Arjun-Saini/loop-tracks/images and diagrams/90 right.png

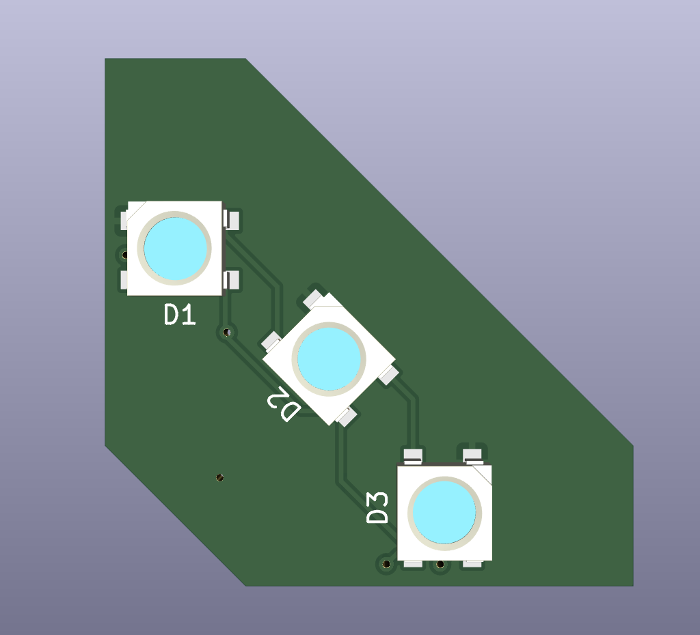
images and diagrams/90 right.png
