Arjun-Saini/loop-tracks/images and diagrams/1.jpeg

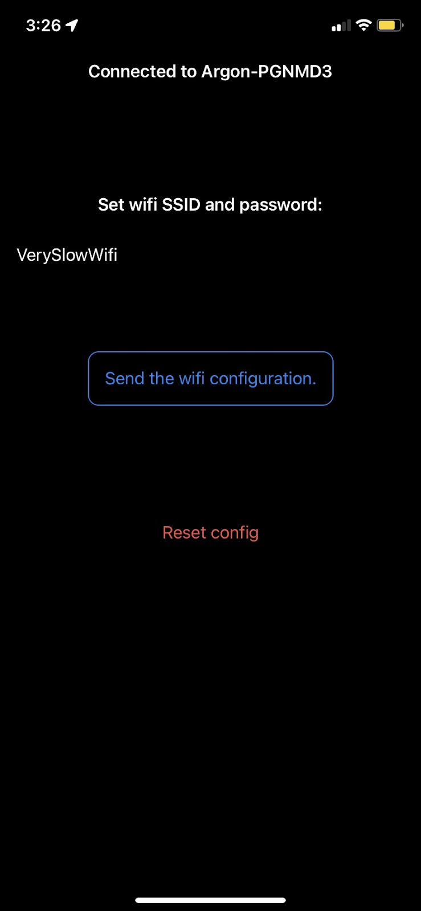
images and diagrams/1.jpeg
