Arjun-Saini/loop-tracks/images and diagrams/2.jpeg

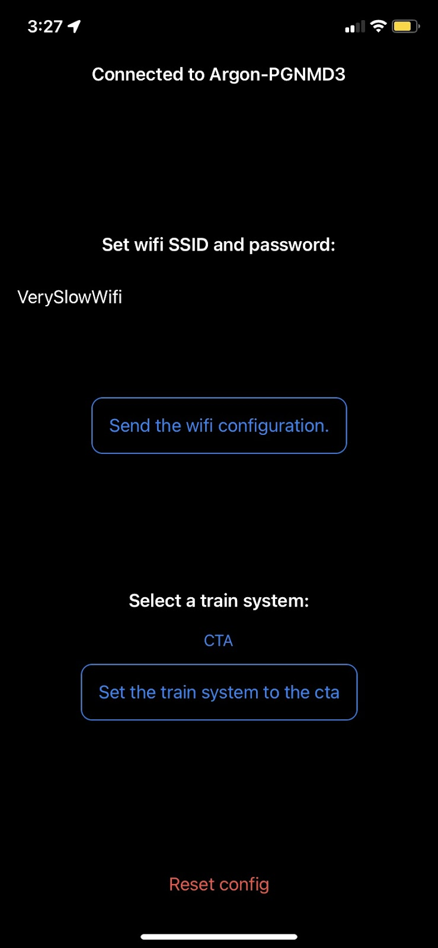
images and diagrams/2.jpeg
