Arjun-Saini/loop-tracks/images and diagrams/3.jpeg

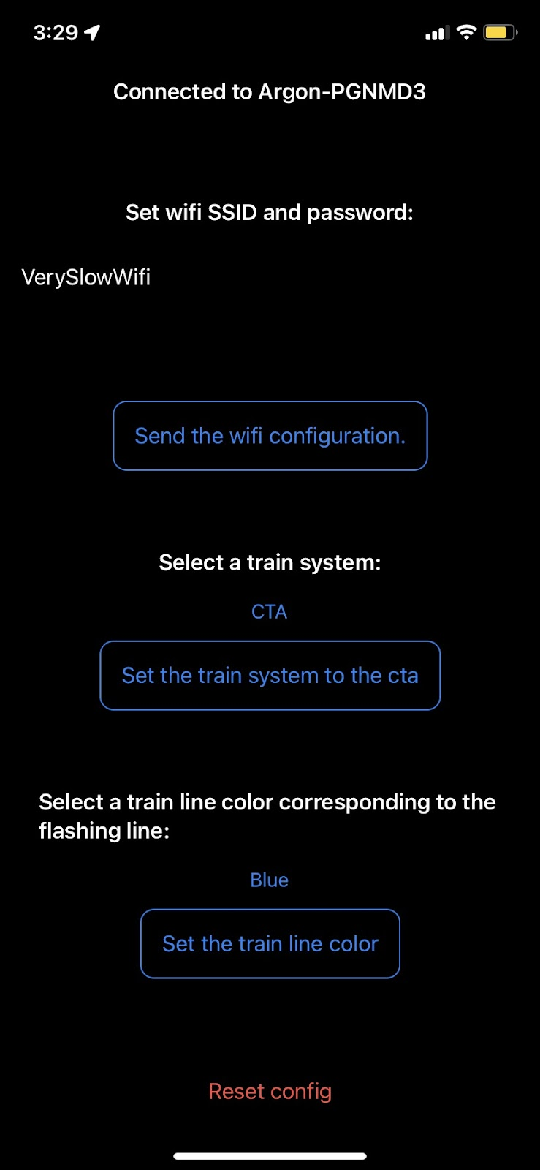
images and diagrams/3.jpeg
