Arjun-Saini/loop-tracks/images and diagrams/90 left.png

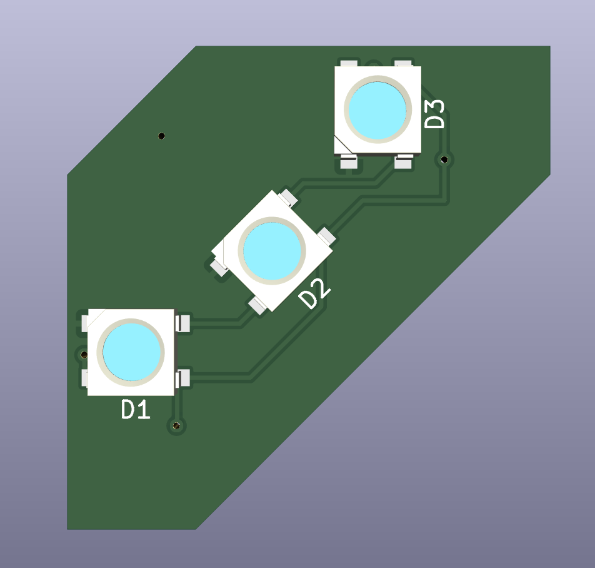
images and diagrams/90 left.png
