Arjun-Saini/loop-tracks/images and diagrams/cta diagram 0.png

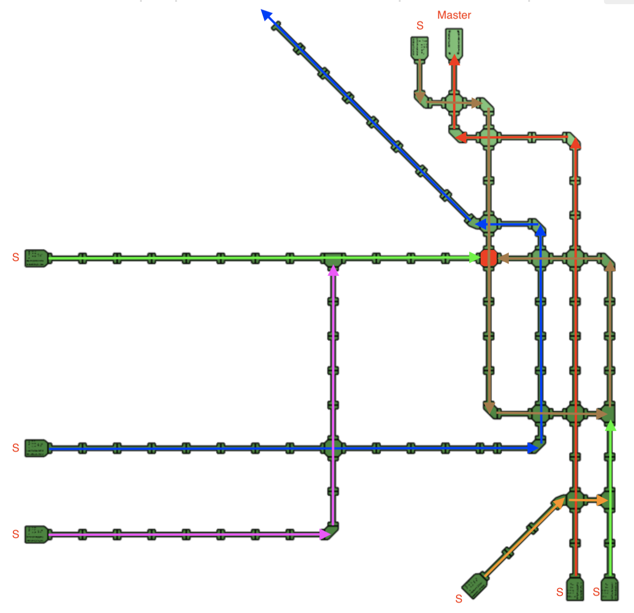
images and diagrams/cta diagram 0.png
