Arjun-Saini/loop-tracks/images and diagrams/cta diagram 1.png

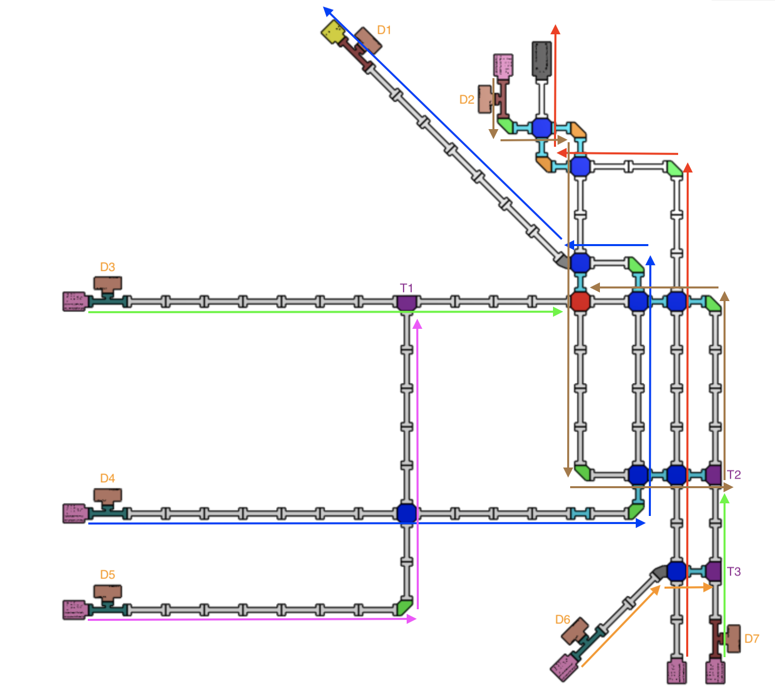
images and diagrams/cta diagram 1.png
