Arjun-Saini/loop-tracks/images and diagrams/cta diagram 4.png

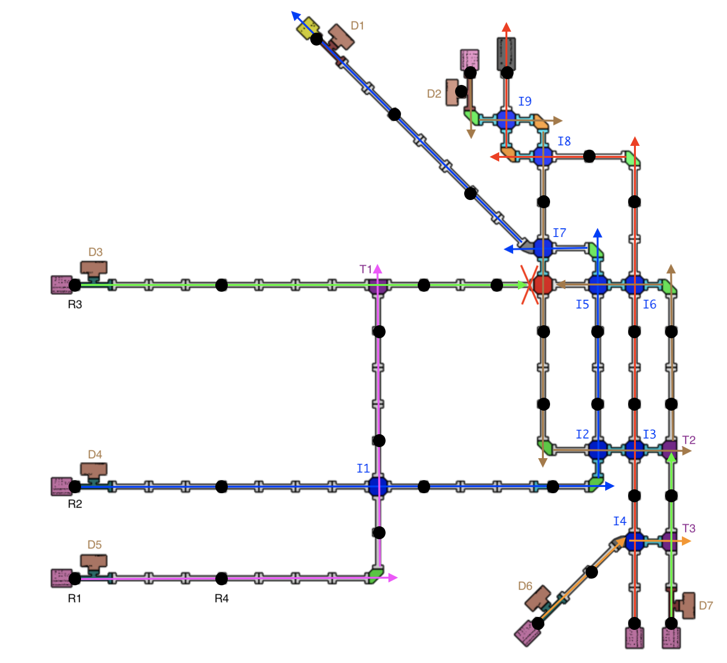
images and diagrams/cta diagram 4.png
