Arjun-Saini/loop-tracks/images and diagrams/intersection.png

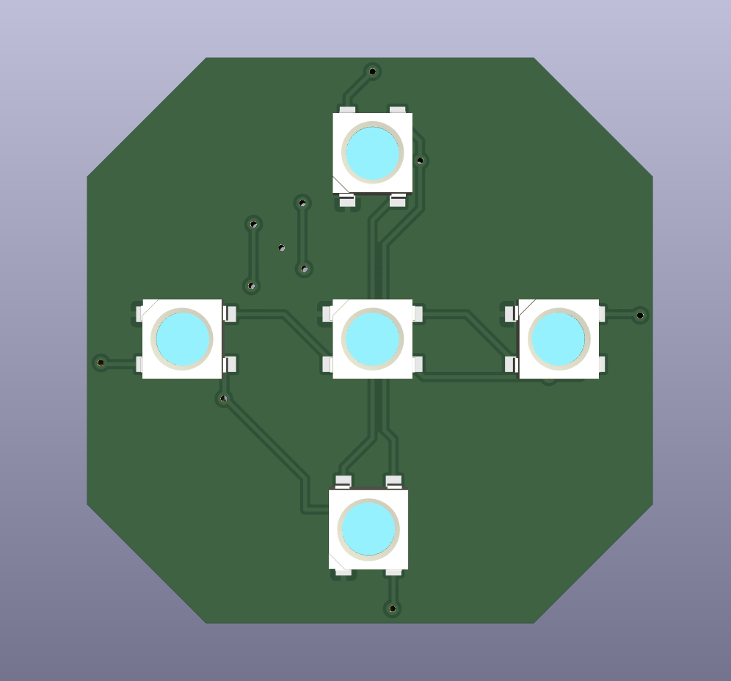
images and diagrams/intersection.png
