Arjun-Saini/loop-tracks/images and diagrams/long straight.png

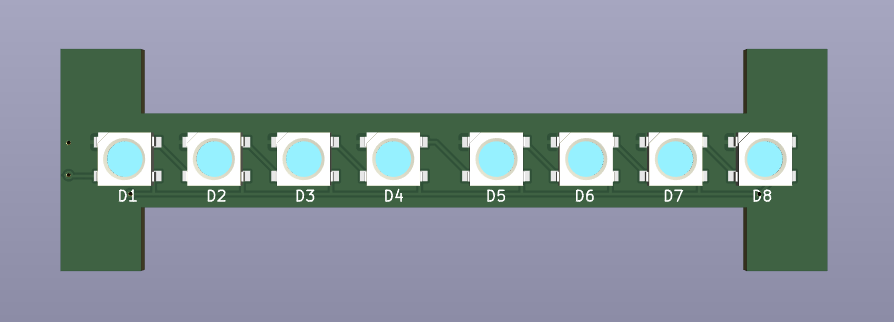
images and diagrams/long straight.png
