Arjun-Saini/loop-tracks/images and diagrams/master mount.png

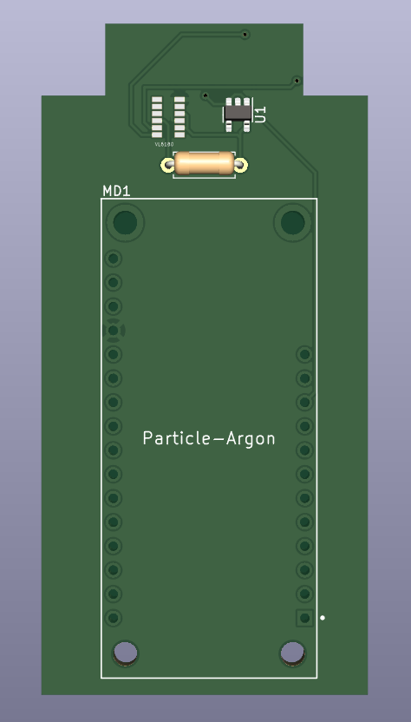
images and diagrams/master mount.png
