Arjun-Saini/loop-tracks/images and diagrams/offshoot left.png

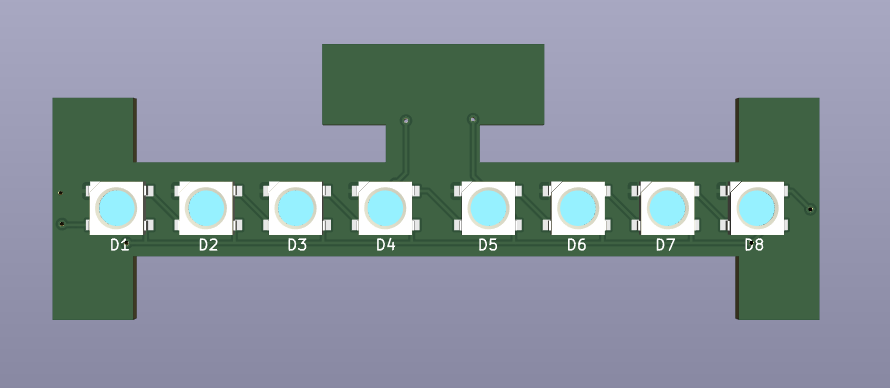
images and diagrams/offshoot left.png
