Arjun-Saini/loop-tracks/images and diagrams/power mount.png

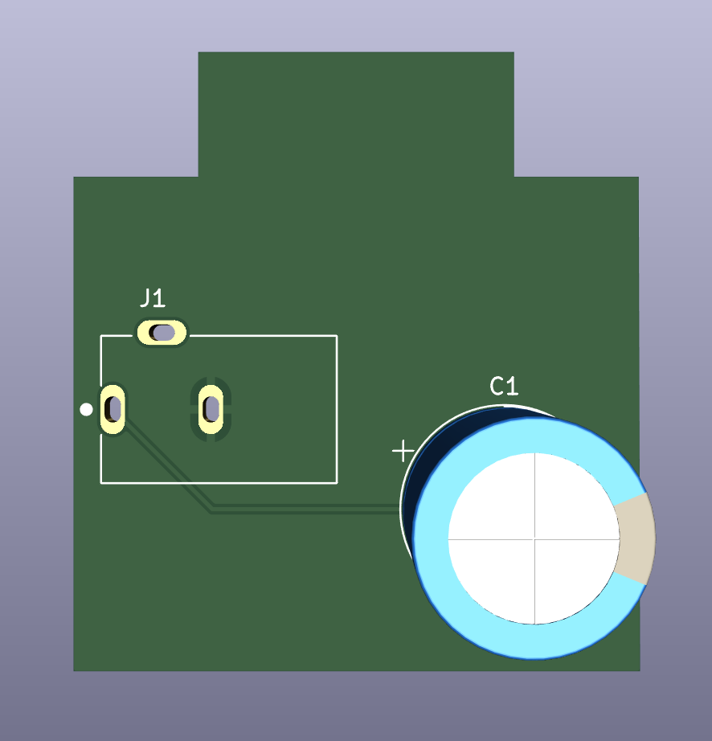
images and diagrams/power mount.png
