Arjun-Saini/loop-tracks/images and diagrams/short straight.png

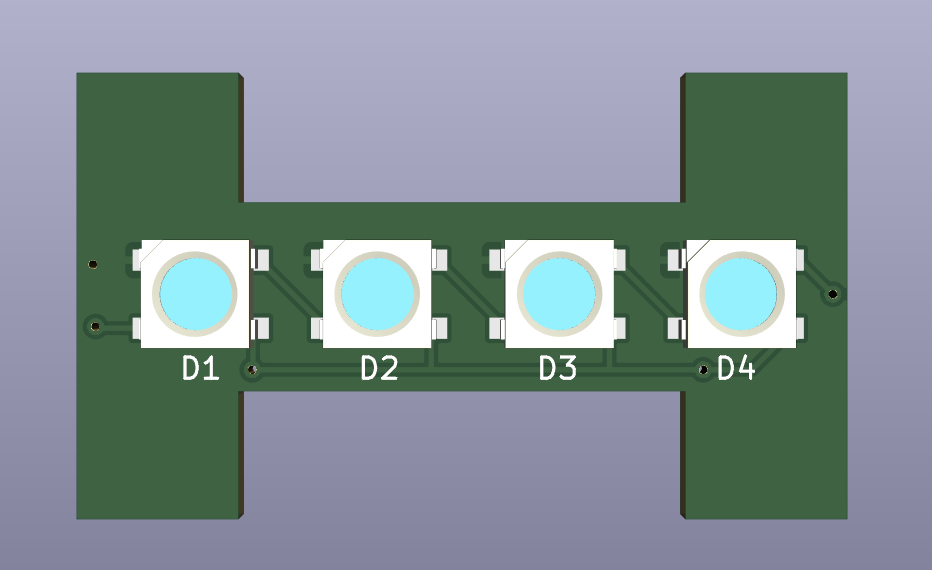
images and diagrams/short straight.png
