Arjun-Saini/loop-tracks/images and diagrams/slave mount.png

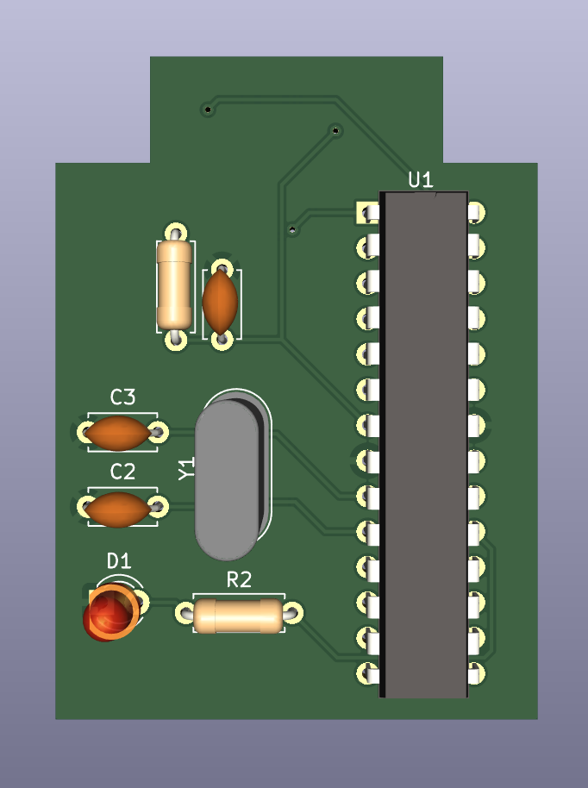
images and diagrams/slave mount.png
