Arjun-Saini/loop-tracks/images and diagrams/standard intersection arrows.png

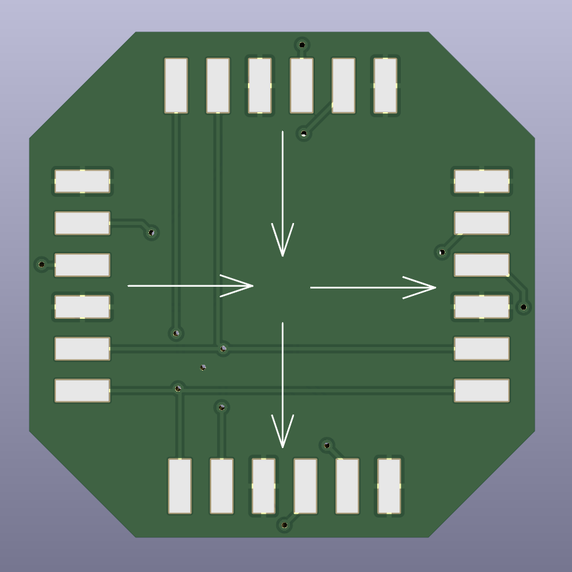
images and diagrams/standard intersection arrows.png
