Arjun-Saini/loop-tracks/images and diagrams/straight left arrows.png

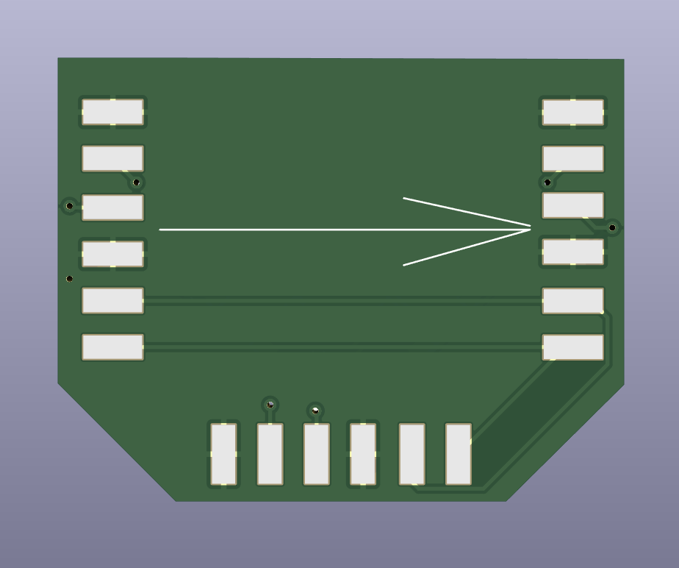
images and diagrams/straight left arrows.png
