Arjun-Saini/loop-tracks/images and diagrams/to left arrows.png

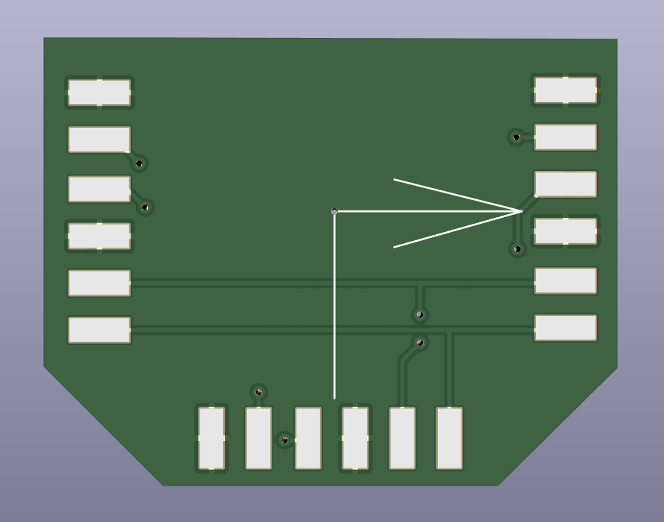
images and diagrams/to left arrows.png
