Arjun-Saini/loop-tracks/images and diagrams/wall mount.png

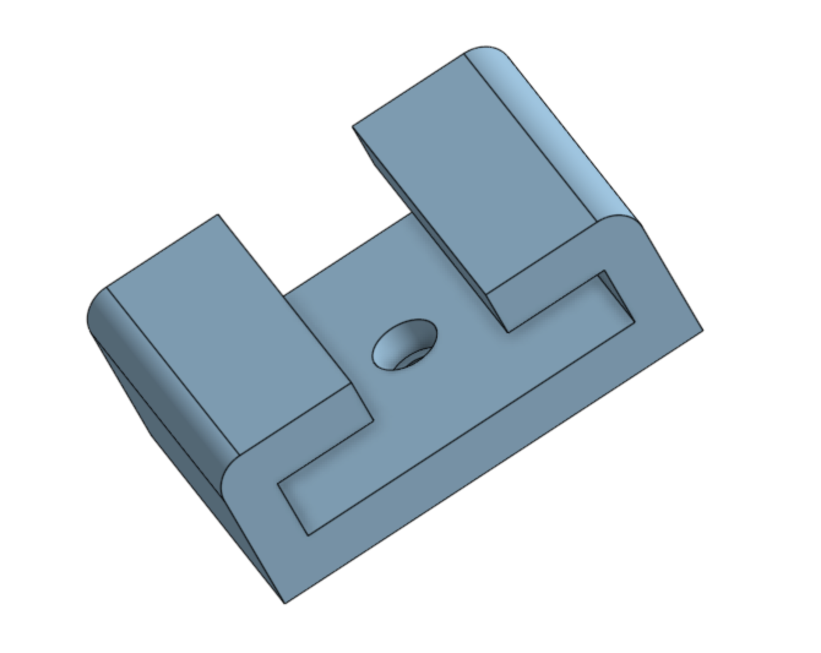
images and diagrams/wall mount.png
