Arjun-Saini/loop-tracks/PCB Design/90deg_left_turn/90deg_left_turn.kicad_pcb

## KiCad design PCB Design/90deg_left_turn/90deg_left_turn.kicad_pcb (2022-08-08)

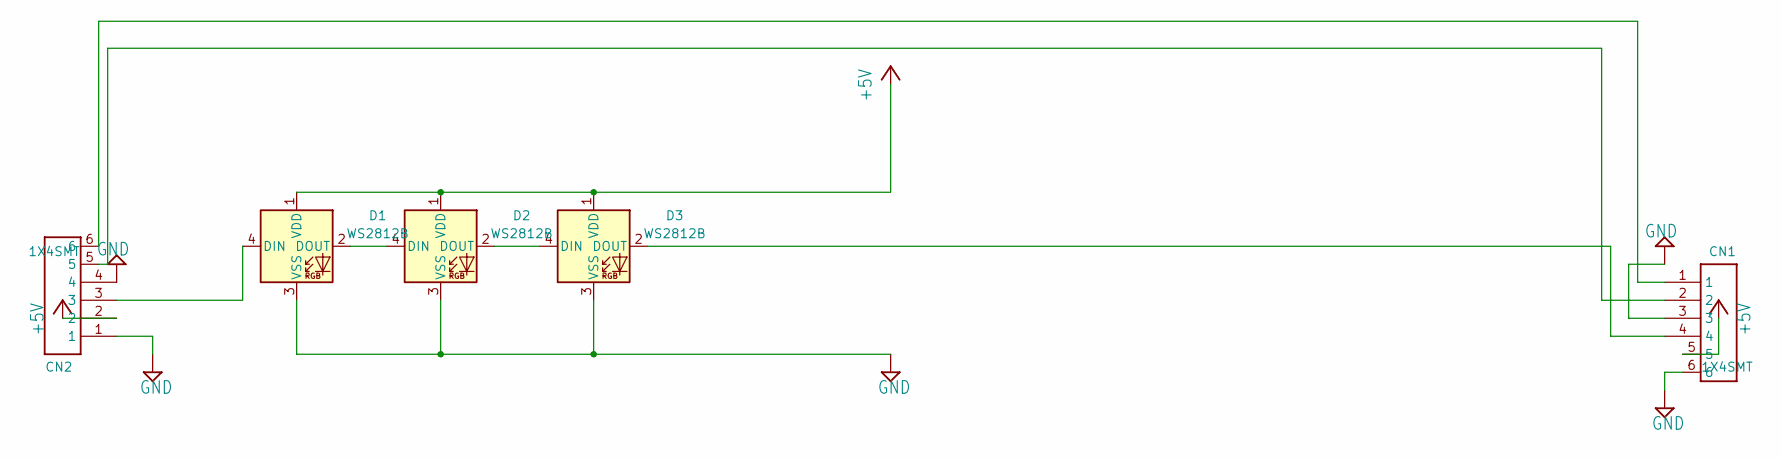
[picture p57: schematic 90deg_left_turn.kicad_sch]

Parts:
CN1, CN2: 1X4SMT; 1X4-SMT
D1, D2, D3: WS2812B; LED_WS2812B_PLCC4_5.0x5.0mm_P3.2mm

Connections:
+5V: CN1.5, CN2.2, D1.1 (VDD), D2.1 (VDD), D3.1 (VDD)
GND: CN1.3, CN1.6, CN2.1, CN2.4, D1.3 (VSS), D2.3 (VSS), D3.3 (VSS)
unnamed: CN1.1, CN2.6
unnamed: CN1.2, CN2.5
unnamed: CN2.3, D1.4 (DIN)
unnamed: D1.2 (DOUT), D2.4 (DIN)
unnamed: D2.2 (DOUT), D3.4 (DIN)
unnamed: CN1.4, D3.2 (DOUT)
