Arjun-Saini/loop-tracks/PCB Design/90deg_left_turn/90deg_left_turn.kicad_pcb

## KiCad design PCB Design/90deg_left_turn/90deg_left_turn.kicad_pcb (continued)

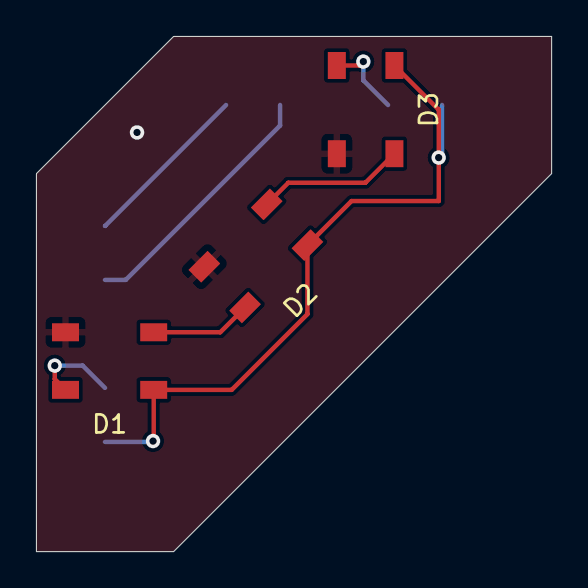
[picture p58: board 90deg_left_turn.kicad_pcb from above]

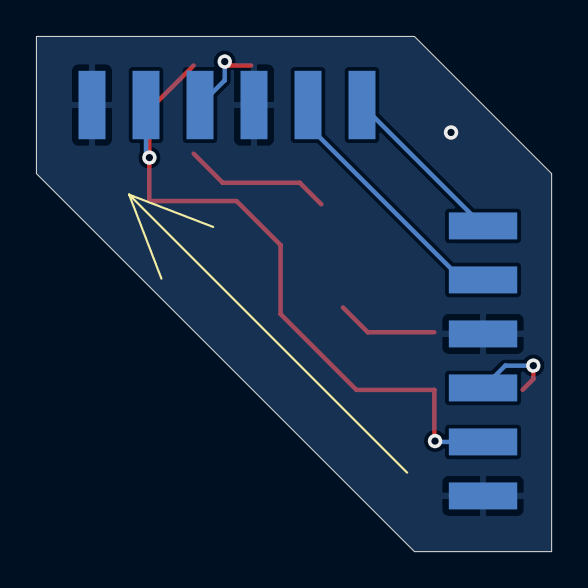
[picture p59: board 90deg_left_turn.kicad_pcb from below]

Board: 2 copper layers, 28.6 x 28.6 mm, 5 parts (2 on the bottom side), 8 nets.
