Arjun-Saini/loop-tracks/PCB Design/14_segment_display/14_segment_display.kicad_pcb

## KiCad design PCB Design/14_segment_display/14_segment_display.kicad_pcb (2022-08-08)

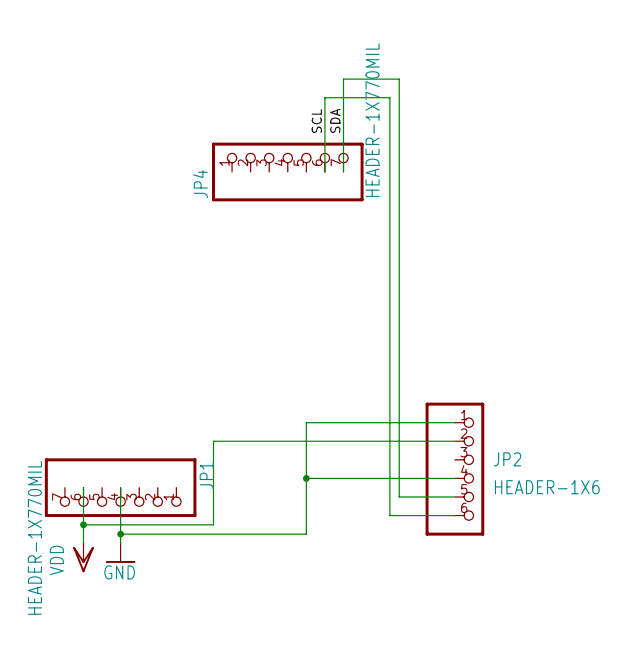
[picture p60: schematic 14_segment_display.kicad_sch]

Parts:
JP1, JP4: HEADER-1X770MIL; 1X07_ROUND_70
JP2: HEADER-1X6; 1X4-SMT

Connections:
/SCL: JP2.6, JP4.6
/SDA: JP2.5, JP4.7
GND: JP1.4, JP2.1, JP2.4
VDD: JP1.6, JP2.2

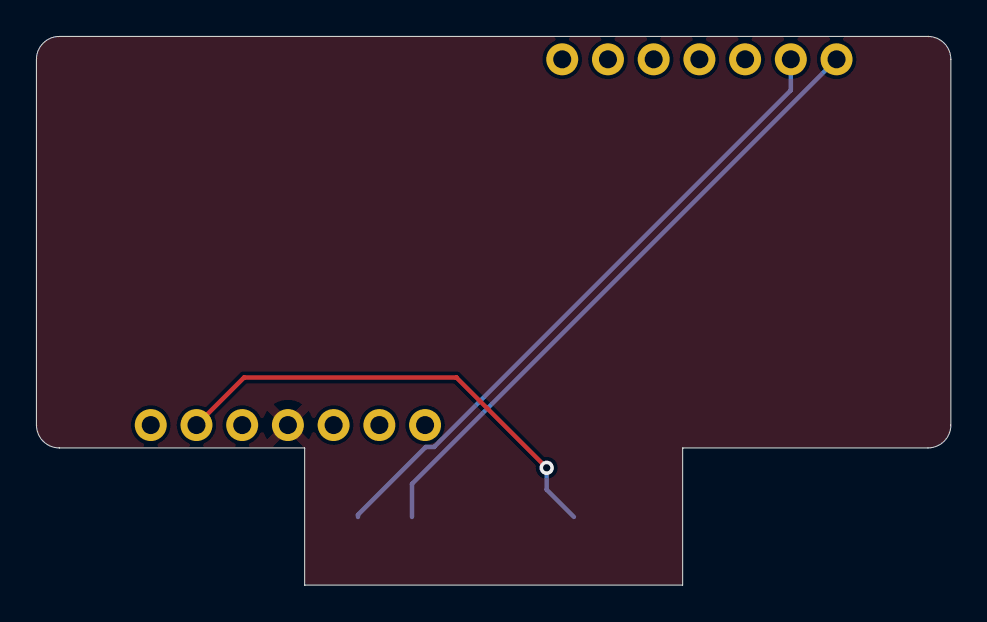
[picture p61: board 14_segment_display.kicad_pcb from above]

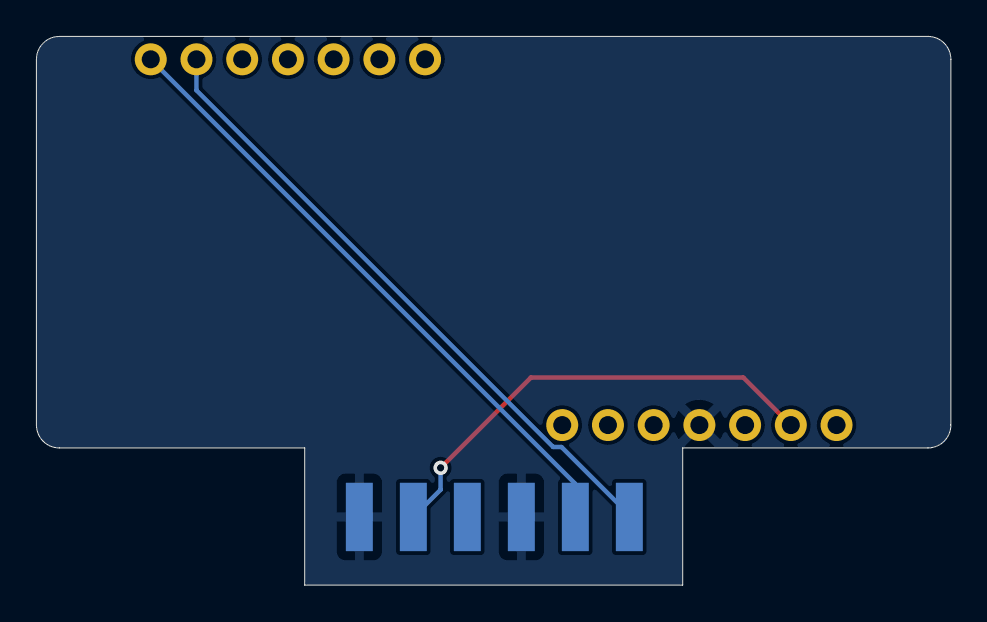
[picture p62: board 14_segment_display.kicad_pcb from below]

Board: 16 copper layers, 50.8 x 30.5 mm, 3 parts (3 on the bottom side), 4 nets.
